wago-enterprise-education/praktikum-gib-mir-mal-ne-wago/images/gibmirmalnewago-keyvisual.jpg

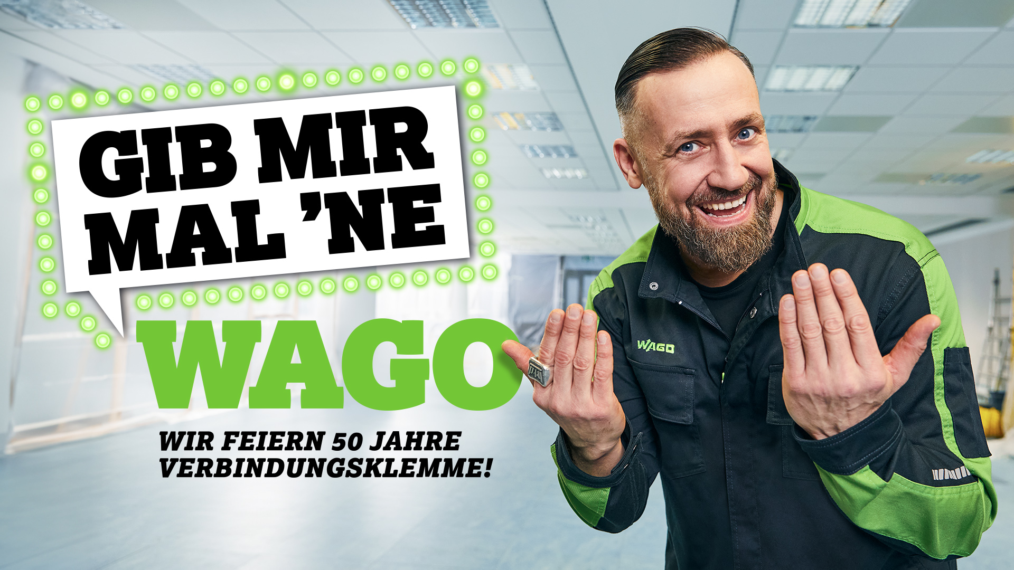
images/gibmirmalnewago-keyvisual.jpg
